LEDs-by-glowingkitty/GlowCore-Mini/images/GlowCoreMini PCB 2 cutout.png

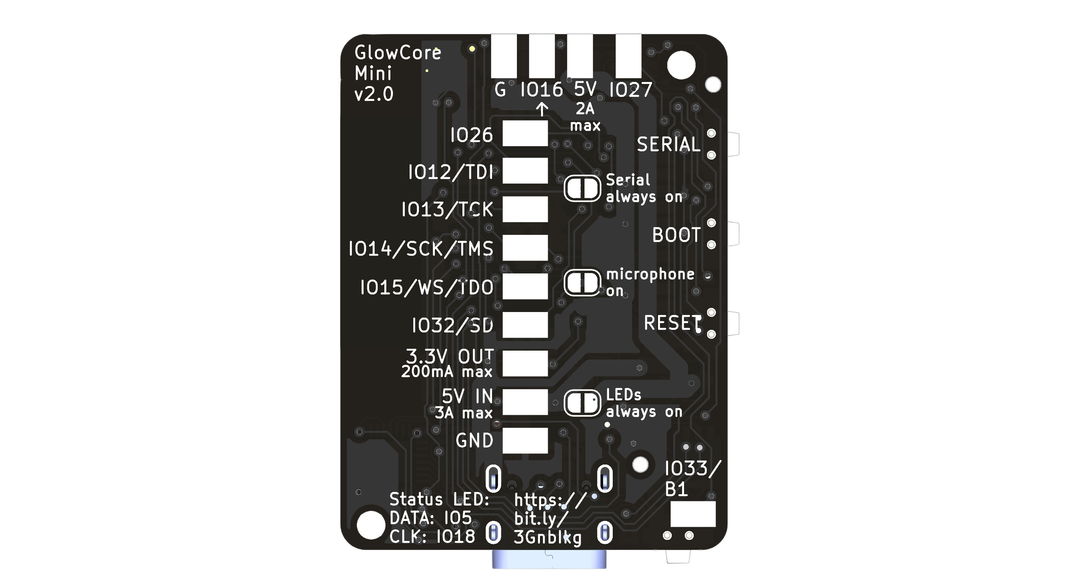
images/GlowCoreMini PCB 2 cutout.png
